feilipu/ux_module/pcb/prototype/RC2014 UX MODULE BRD.png

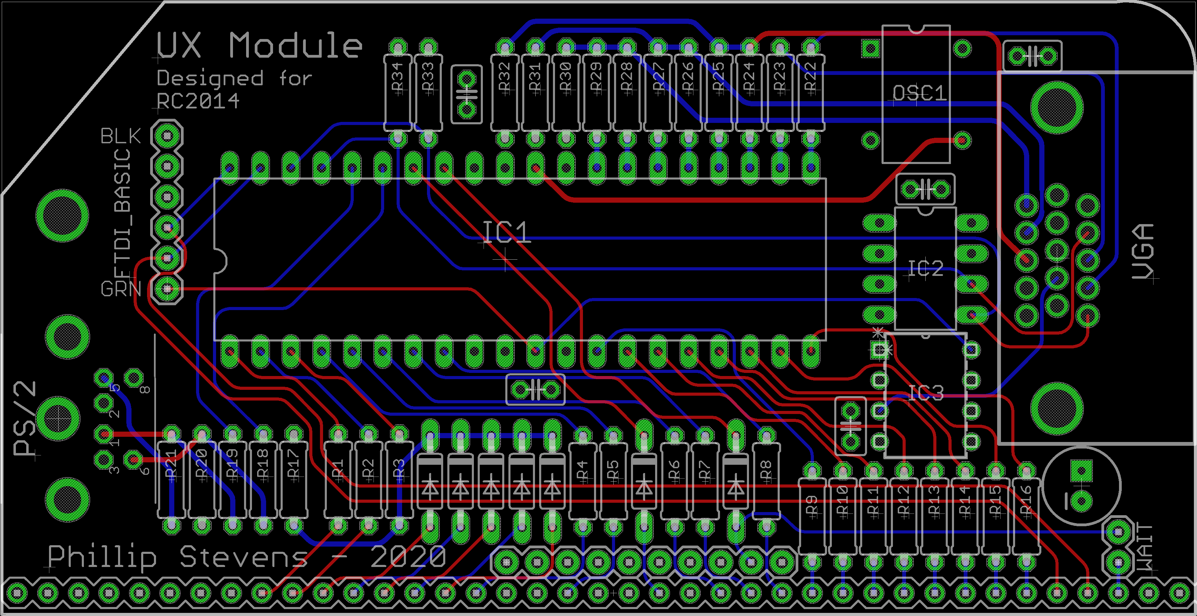
pcb/prototype/RC2014 UX MODULE BRD.png
