feilipu/ux_module/pcb/prototype/RC2014 UX MODULE VALUES.png

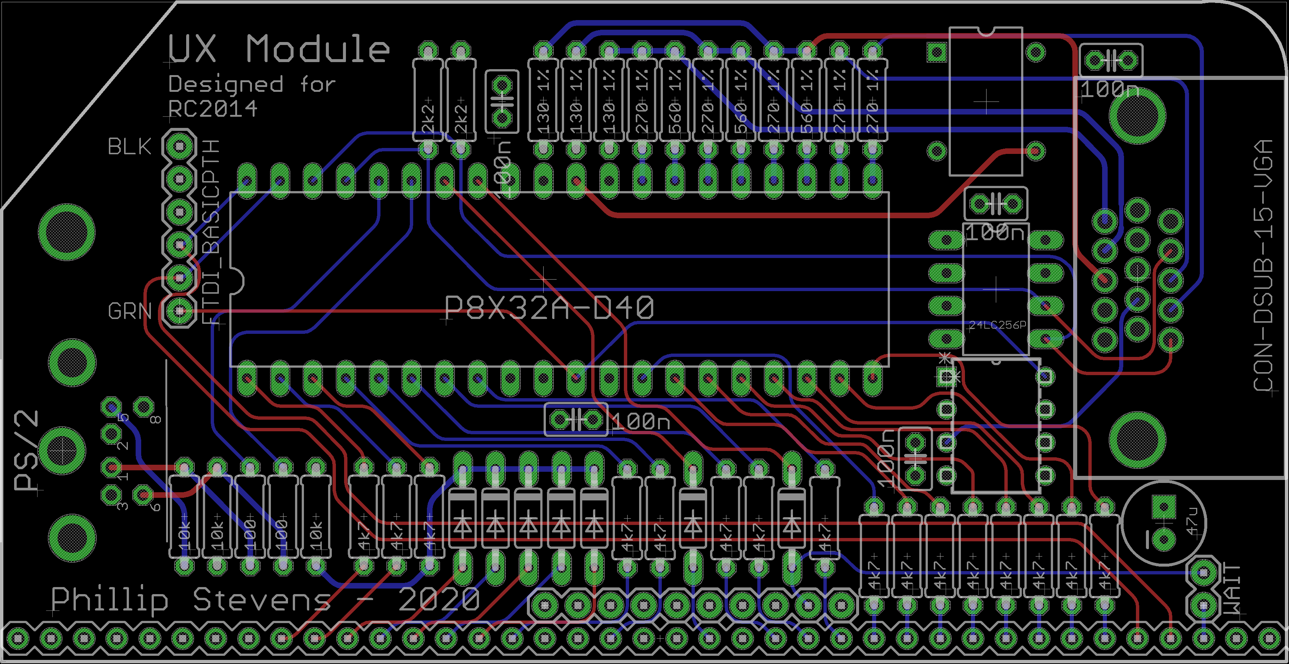
pcb/prototype/RC2014 UX MODULE VALUES.png
