feilipu/ux_module/pcb/RC2014_UX_MODULE_VALUES.png

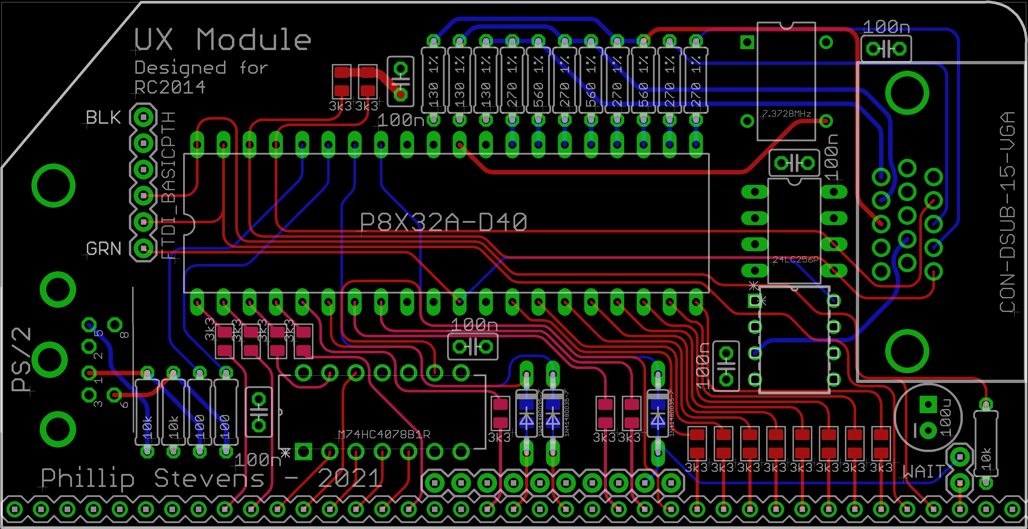
pcb/RC2014_UX_MODULE_VALUES.png
